AshitakaLax/Ultimate_Developer_Keyboard/Software/embeddedCode/simpleBoard/SimpleKeyBoard/SimpleKeyBoard/src/main.c

/**
 * \file
 *
 * \brief Main functions for USB composite example
 *
 * Copyright (c) 2009-2015 Atmel Corporation. All rights reserved.
 *
 * \asf_license_start
 *
 * \page License
 *
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
 * 3. The name of Atmel may not be used to endorse or promote products derived
 *    from this software without specific prior written permission.
 *
 * 4. This software may only be redistributed and used in connection with an
 *    Atmel microcontroller product.
 *
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
 * \asf_license_stop
 *
 */
/*
 * Support and FAQ: visit <a href="http://www.atmel.com/design-support/">Atmel Support</a>
 */

#include <asf.h>
#include "conf_usb.h"
#include "ui.h"
#include "uart.h"

static volatile bool main_b_keyboard_enable = false;
static volatile bool main_b_mouse_enable = false;
static volatile bool main_b_msc_enable = false;
static volatile bool main_b_cdc_enable = false;

/*! \brief Main function. Execution starts here.
 */
int main(void)//
{
	irq_initialize_vectors();
	cpu_irq_enable();

	// Initialize the sleep manager
	//sleepmgr_init();
#if !SAMD21 && !SAMR21 && !SAML21
	sysclk_init();
	board_init();
#else
	system_init();
#endif
	ui_init();
	ui_powerdown();

	memories_initialization();

	// Start USB stack to authorize VBus monitoring
	udc_start();

	// The main loop manages only the power mode
	// because the USB management is done by interrupt
	while (true) {

	//this is just an attempt to
	static volatile uint16_t virtual_sof_sub = 0;
	
	if (udd_get_frame_number()/500 == virtual_sof_sub++) 
	{
		virtual_sof_sub = 0;
		static uint16_t virtual_sof = 0;
		ui_process(virtual_sof++);
	}
	
//	ui_process(udd_get_frame_number());
	
		//if (main_b_msc_enable) {
			//if (!udi_msc_process_trans()) {
				//sleepmgr_enter_sleep();
			//}
		//}else{
			sleepmgr_enter_sleep();
		//}
	}
}

void main_suspend_action(void)
{
	ui_powerdown();
}

void main_resume_action(void)
{
	ui_wakeup();
}

void main_sof_action(void)
{
	if ((!main_b_mouse_enable) ||
		(!main_b_msc_enable) ||
		(!main_b_keyboard_enable) ||
		(!main_b_cdc_enable))
		return;
	ui_process(udd_get_frame_number());
}

void main_remotewakeup_enable(void)
{
	ui_wakeup_enable();
}

void main_remotewakeup_disable(void)
{
	ui_wakeup_disable();
}

/*! \brief Example of extra USB string management
 * This feature is available for single or composite device
 * which want implement additional USB string than
 * Manufacture, Product and serial number ID.
 *
 * return true, if the string ID requested is know and managed by this functions
 */
bool main_extra_string(void)
{
	static uint8_t udi_cdc_name[] = "CDC interface";
	static uint8_t udi_msc_name[] = "MSC interface";
	static uint8_t udi_hid_mouse_name[] = "HID mouse interface";
	static uint8_t udi_hid_kbd_name[] = "HID keyboard interface";

	struct extra_strings_desc_t{
		usb_str_desc_t header;
		le16_t string[Max(Max(Max( \
			sizeof(udi_cdc_name)-1, sizeof(udi_msc_name)-1),\
			sizeof(udi_hid_mouse_name)-1), sizeof(udi_hid_kbd_name)-1)];
	};
	static UDC_DESC_STORAGE struct extra_strings_desc_t extra_strings_desc = {
		.header.bDescriptorType = USB_DT_STRING
	};

	uint8_t i;
	uint8_t *str;
	uint8_t str_lgt=0;

	// Link payload pointer to the string corresponding at request
	switch (udd_g_ctrlreq.req.wValue & 0xff) {
	case UDI_CDC_IAD_STRING_ID:
		str_lgt = sizeof(udi_cdc_name)-1;
		str = udi_cdc_name;
		break;
	case UDI_MSC_STRING_ID:
		str_lgt = sizeof(udi_msc_name)-1;
		str = udi_msc_name;
		break;
	case UDI_HID_MOUSE_STRING_ID:
		str_lgt = sizeof(udi_hid_mouse_name)-1;
		str = udi_hid_mouse_name;
		break;
	case UDI_HID_KBD_STRING_ID:
		str_lgt = sizeof(udi_hid_kbd_name)-1;
		str = udi_hid_kbd_name;
		break;
	default:
		return false;
	}

	if (str_lgt!=0) {
		for( i=0; i<str_lgt; i++) {
			extra_strings_desc.string[i] = cpu_to_le16((le16_t)str[i]);
		}
		extra_strings_desc.header.bLength = 2+ (str_lgt)*2;
		udd_g_ctrlreq.payload_size = extra_strings_desc.header.bLength;
		udd_g_ctrlreq.payload = (uint8_t *) &extra_strings_desc;
	}

	// if the string is larger than request length, then cut it
	if (udd_g_ctrlreq.payload_size > udd_g_ctrlreq.req.wLength) {
		udd_g_ctrlreq.payload_size = udd_g_ctrlreq.req.wLength;
	}
	return true;
}

bool main_msc_enable(void)
{
	main_b_msc_enable = true;
	return true;
}

void main_msc_disable(void)
{
	main_b_msc_enable = false;
}

bool main_mouse_enable(void)
{
	main_b_mouse_enable = true;
	return true;
}

void main_mouse_disable(void)
{
	main_b_mouse_enable = false;
}

bool main_keyboard_enable(void)
{
	main_b_keyboard_enable = true;
	return true;
}

void main_keyboard_disable(void)
{
	main_b_keyboard_enable = false;
}

bool main_cdc_enable(uint8_t port)
{
	main_b_cdc_enable = true;
	// Open communication
	uart_open(port);
	return true;
}

void main_cdc_disable(uint8_t port)
{
	main_b_cdc_enable = false;
	// Close communication
	uart_close(port);
}

void main_cdc_set_dtr(uint8_t port, bool b_enable)
{
	if (b_enable) {
		// Host terminal has open COM
		ui_com_open(port);
	}else{
		// Host terminal has close COM
		ui_com_close(port);
	}
}

/**
 * \mainpage ASF USB Composite Device Example HIDs, CDC and MSC
 *
 * \section intro Introduction
 * This example shows how to implement a USB Composite Device with HID mouse,
 * keyboard, CDC and Mass Storage interfaces on Atmel MCU with USB module.
 *
 * \section desc Description of the Communication Device Class (CDC)
 * The Communication Device Class (CDC) is a general-purpose way to enable all
 * types of communications on the Universal Serial Bus (USB).
 * This class makes it possible to connect communication devices such as
 * digital telephones or analog modems, as well as networking devices
 * like ADSL or Cable modems.
 * While a CDC device enables the implementation of quite complex devices,
 * it can also be used as a very simple method for communication on the USB.
 * For example, a CDC device can appear as a virtual COM port, which greatly
 * simplifies application development on the host side.
 *
 * \section startup Startup
 * The example uses all memories available on the board and connects these to
 * USB Device Mass Storage stack.
 * Also, the example is a bridge between a USART from the main MCU
 * and the USB CDC interface.
 * And, the example uses the buttons or sensors available on the board
 * to simulate a standard mouse, keyboard.
 * After loading firmware, connect the board (EVKxx,Xplain,...) to the USB Host.
 * When connected to a USB host system this application allows to display
 * all available memories as a removable disks and provides a mouse in
 * the Unix/Mac/Windows operating systems.
 *
 * For USB to UART bridge:
 * - Connect the USART peripheral to the USART interface of the board.
 * - Connect the application to a USB host (e.g. a PC)
 *   with a mini-B (embedded side) to A (PC host side) cable.
 * The application will behave as a virtual COM (see Windows Device Manager).
 * - Open a HyperTerminal on both COM ports (RS232 and Virtual COM)
 * - Select the same configuration for both COM ports up to 115200 baud.
 * - Type a character in one HyperTerminal and it will echo in the other.
 *
 * \note
 * This example uses the native MSC and HID drivers on Unix/Mac/Windows OS, except for Win98.
 * About CDC, on the first connection of the board on the PC,
 * the operating system will detect a new peripheral:
 * - This will open a new hardware installation window.
 * - Choose "No, not this time" to connect to Windows Update for this installation
 * - click "Next"
 * - When requested by Windows for a driver INF file, select the
 *   atmel_devices_cdc.inf file in the directory indicated in the Atmel Studio
 *   "Solution Explorer" window.
 * - click "Next"
 *
 * \copydoc UI
 *
 * \section example About example
 *
 * The example uses the following module groups:
 * - Basic modules:
 *   Startup, board, clock, interrupt, power management
 * - USB Device stack and HID, CDC and MSC modules:
 *   <br>services/usb/
 *   <br>services/usb/udc/
 *   <br>services/usb/class/msc/
 *   <br>services/usb/class/cdc/
 *   <br>services/usb/class/hid/
 *   <br>services/usb/class/hid/mouse/
 *   <br>services/usb/class/hid/keyboard/
 * - Specific implementation:
 *    - main.c,
 *      <br>initializes clock
 *      <br>initializes interrupt
 *      <br>manages UI
 *    - udi_composite_desc.c,udi_composite_conf.h,
 *      <br>USB Composite Device definition
 *    - uart_xmega.c,
 *      <br>implementation of RS232 bridge for XMEGA parts
 *    - uart_uc3.c,
 *      <br>implementation of RS232 bridge for UC3 parts
 *    - uart_sam.c,
 *      <br>implementation of RS232 bridge for SAM parts
 *    - specific implementation for each target "./examples/product_board/":
 *       - conf_foo.h   configuration of each module
 *       - ui.c        implement of user's interface (buttons, leds)
 *
 * <SUP>1</SUP> The memory data transfers are done outside USB interrupt routine.
 * This is done in the MSC process ("udi_msc_process_trans()") called by main loop.
 */
